xJacksee/VU_Meter_Deck/images/device/20220401_185417.jpg

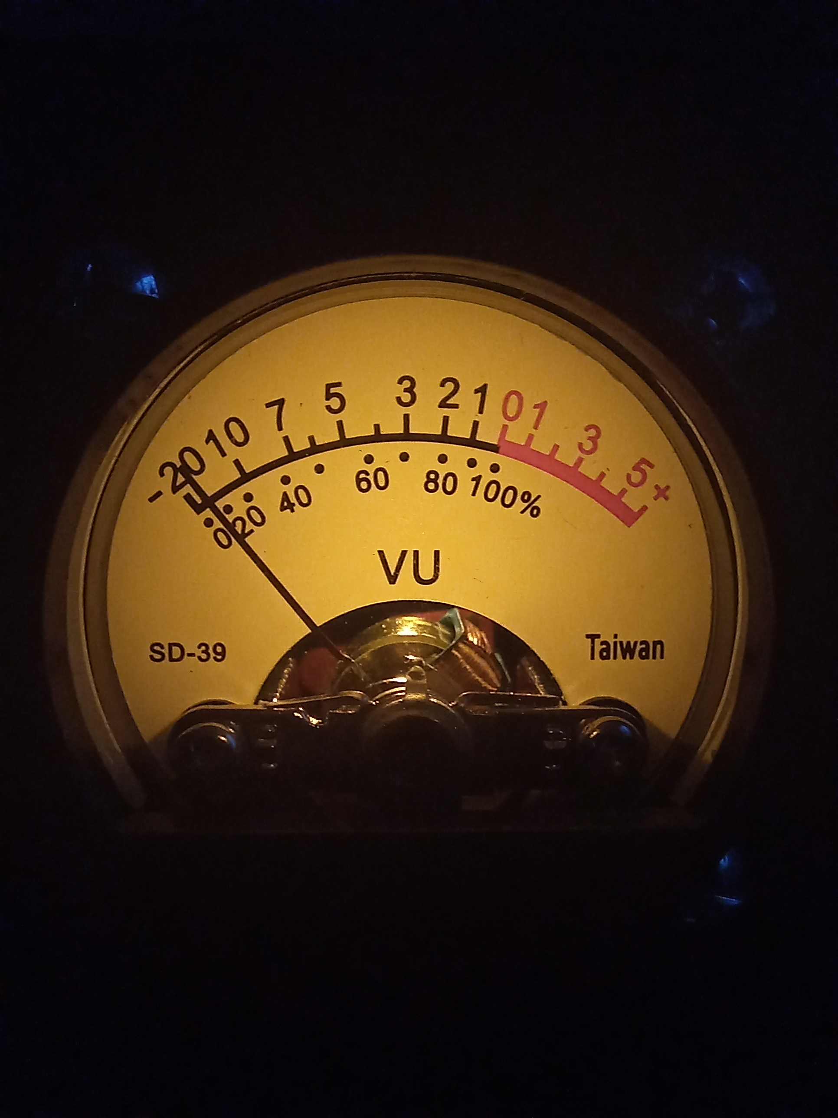
images/device/20220401_185417.jpg
